HenrikSamuelsson/Killer-Bot-2016/AutodeskWorkspace/robotparts revision 2/bottomSideFrame1.stl

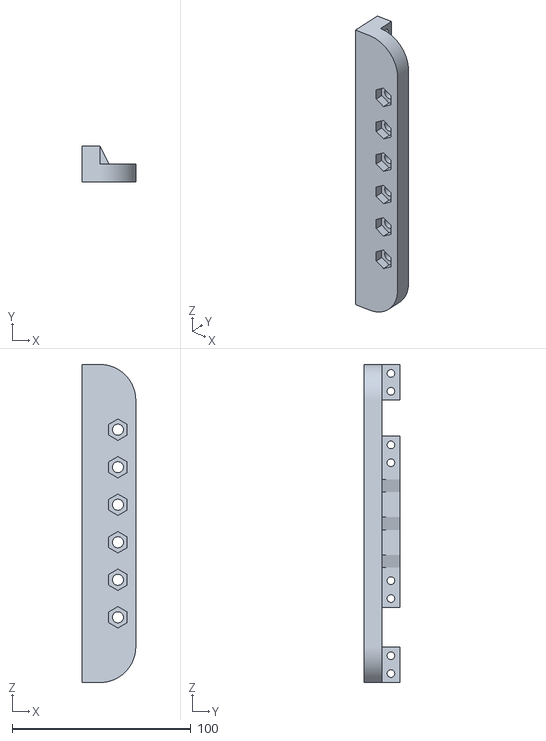
[picture p16: CAD file, 2016-06-10]
AutodeskWorkspace/robotparts revision 2/bottomSideFrame1.stl
30.0 x 20.0 x 178.0
