HenrikSamuelsson/Killer-Bot-2016/printfiles/motorHolder57mm.stl

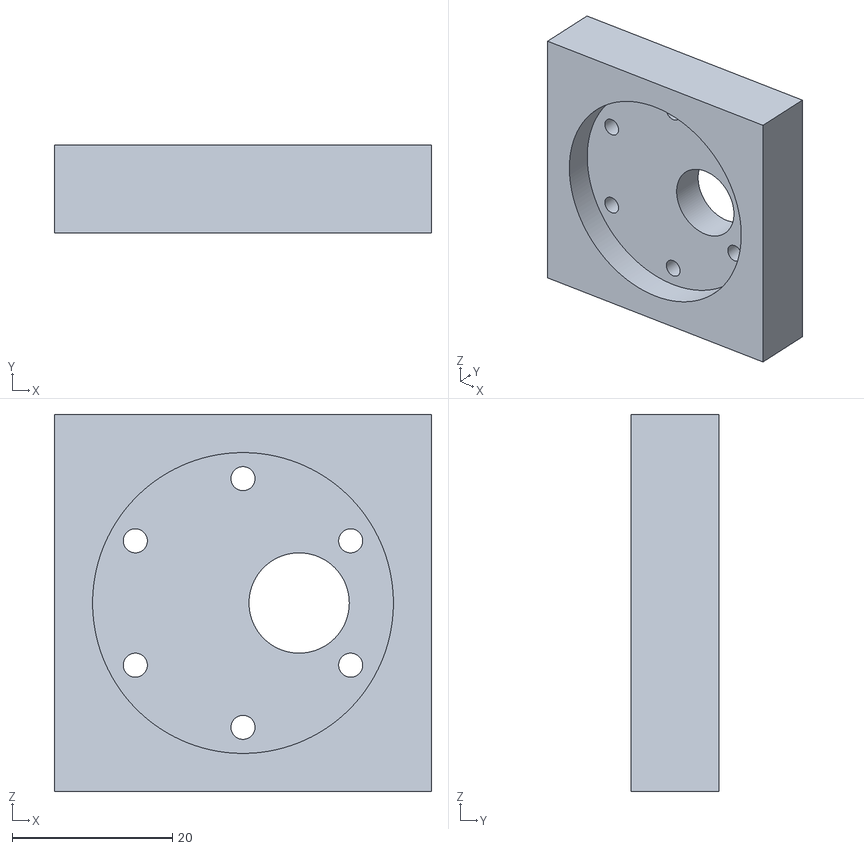
[picture p17: CAD file, 2016-05-10]
printfiles/motorHolder57mm.stl
47.0 x 11.0 x 47.0
