HenrikSamuelsson/Killer-Bot-2016/AutodeskWorkspace/robotparts revision 2/bigOuterSprocket.stl

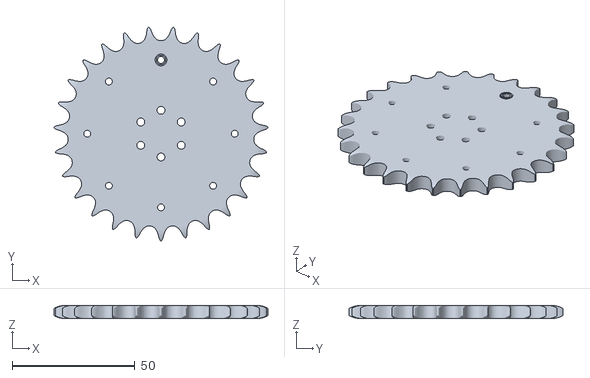
[picture p18: CAD file, 2016-06-10]
AutodeskWorkspace/robotparts revision 2/bigOuterSprocket.stl
87.1 x 86.9 x 5.32
