HenrikSamuelsson/Killer-Bot-2016/printfiles/tracks_outer.stl

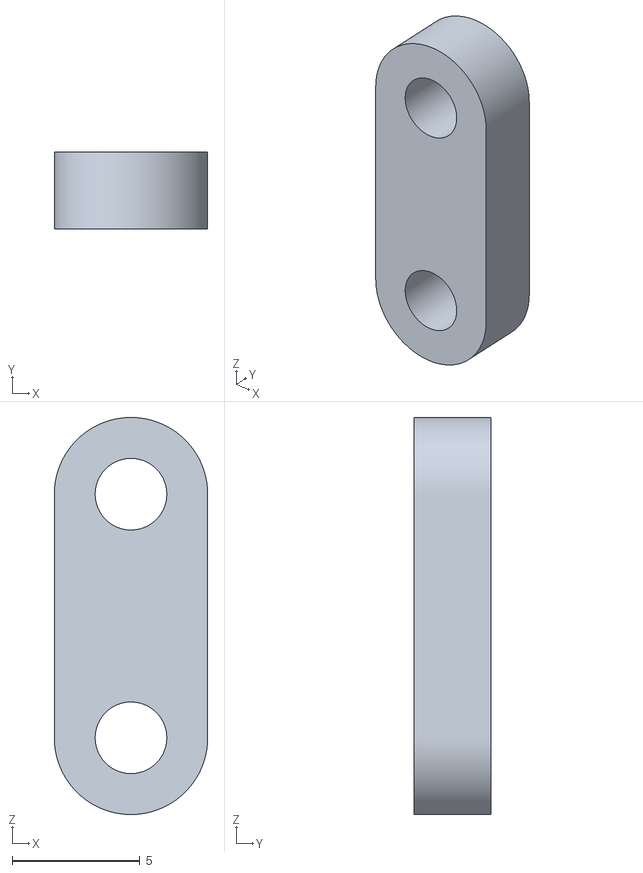
[picture p19: CAD file, 2016-05-04]
printfiles/tracks_outer.stl
6.00 x 3.00 x 15.5
