HenrikSamuelsson/Killer-Bot-2016/AutodeskWorkspace/robotparts revision 2/sideFrame.stl

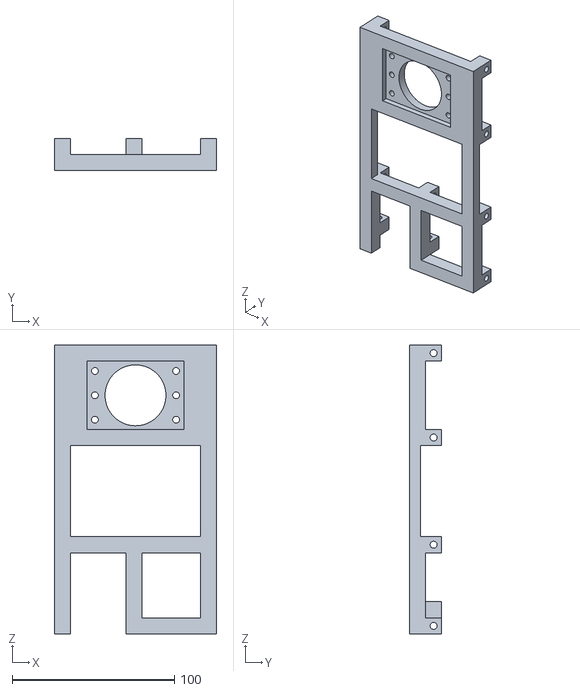
[picture p20: CAD file, 2016-06-08]
AutodeskWorkspace/robotparts revision 2/sideFrame.stl
100.0 x 20.0 x 178.0
