HenrikSamuelsson/Killer-Bot-2016/printfiles/driveSprocket.stl

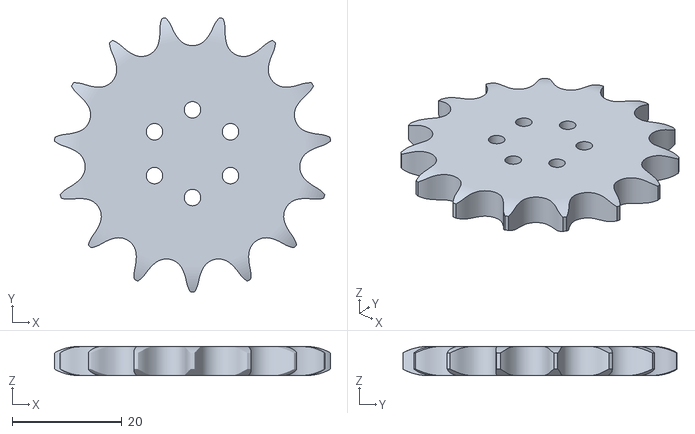
[picture p21: CAD file, 2016-04-27]
printfiles/driveSprocket.stl
50.3 x 50.0 x 5.32
