HenrikSamuelsson/Killer-Bot-2016/printfiles/tracks.stl

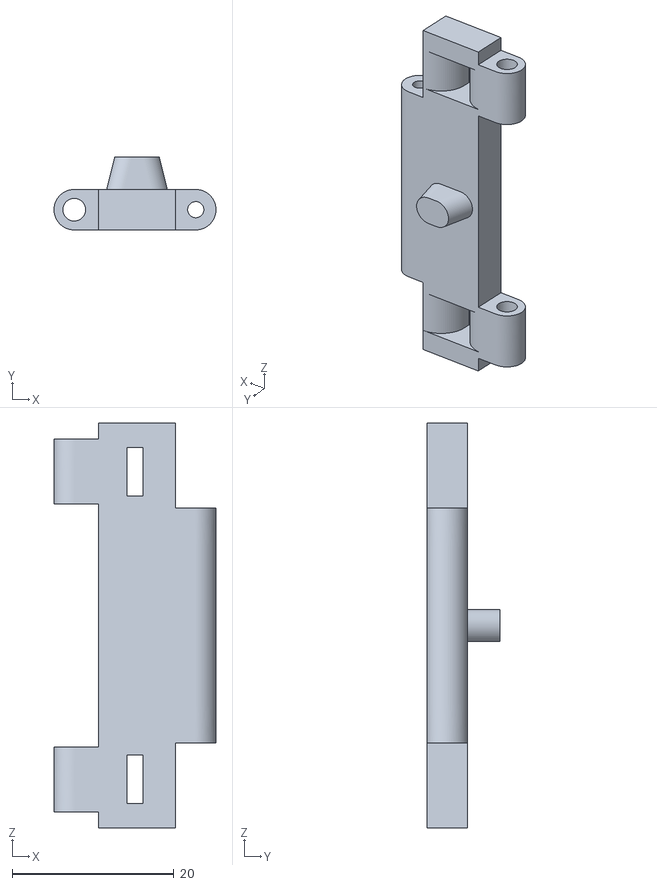
[picture p22: CAD file, 2016-04-20]
printfiles/tracks.stl
20.0 x 9.00 x 50.0
