HenrikSamuelsson/Killer-Bot-2016/AutodeskWorkspace/robotparts revision 2/rollerdistance.stl

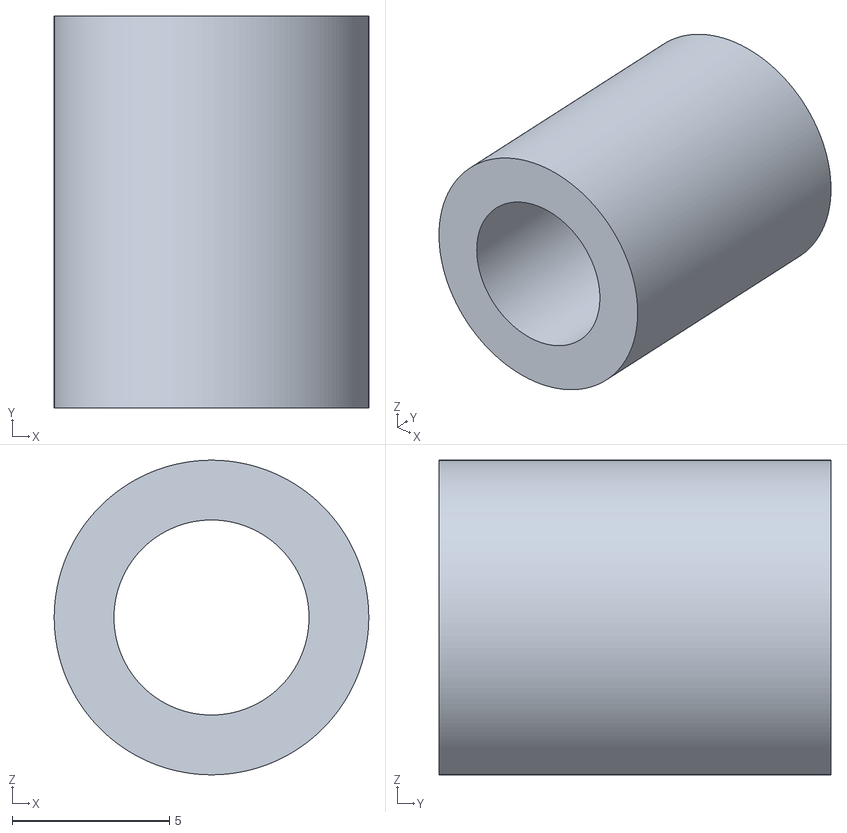
[picture p23: CAD file, 2016-06-06]
AutodeskWorkspace/robotparts revision 2/rollerdistance.stl
10.0 x 12.5 x 10.00
