HenrikSamuelsson/Killer-Bot-2016/printfiles/servoHolderTest1.stl

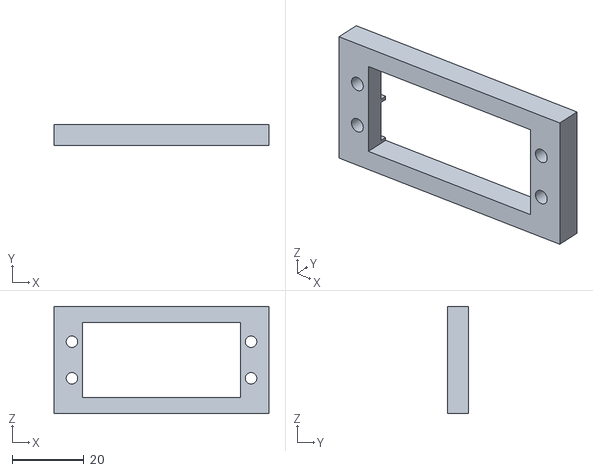
[picture p24: CAD file, 2016-04-17]
printfiles/servoHolderTest1.stl
60.0 x 6.00 x 30.0
