HenrikSamuelsson/Killer-Bot-2016/AutodeskWorkspace/robotparts revision 2/smallSprocketDistance.stl

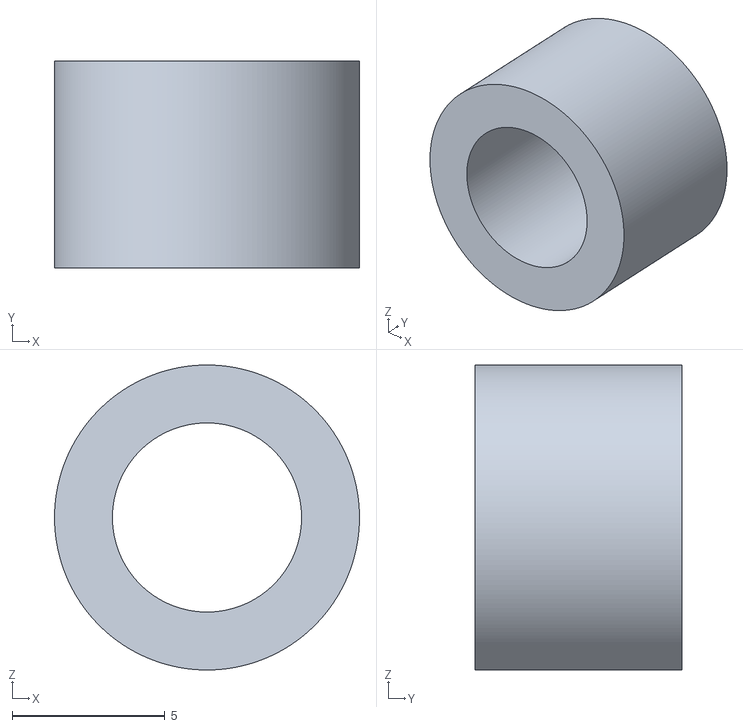
[picture p25: CAD file, 2016-06-06]
AutodeskWorkspace/robotparts revision 2/smallSprocketDistance.stl
10.0 x 6.80 x 10.00
