HenrikSamuelsson/Killer-Bot-2016/AutodeskWorkspace/robotparts revision 2/backFrame.stl

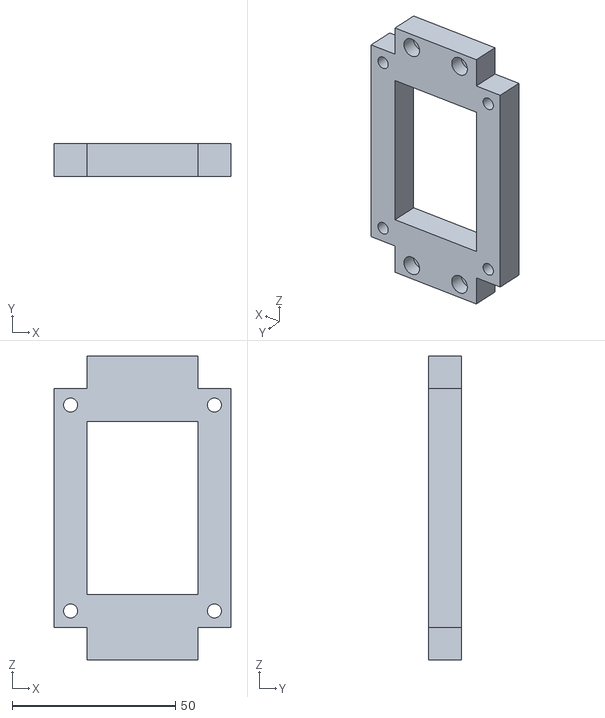
[picture p26: CAD file, 2016-06-06]
AutodeskWorkspace/robotparts revision 2/backFrame.stl
54.0 x 10.0 x 93.0
