HenrikSamuelsson/Killer-Bot-2016/AutodeskWorkspace/robotparts revision 2/smallSprocketFixture.stl

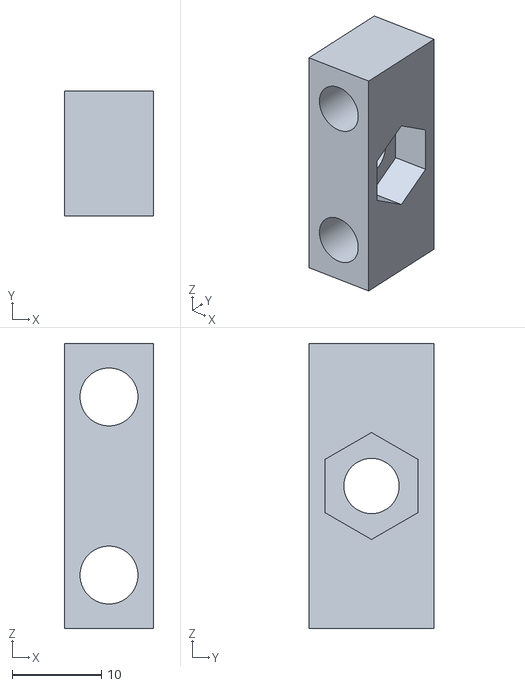
[picture p27: CAD file, 2016-06-06]
AutodeskWorkspace/robotparts revision 2/smallSprocketFixture.stl
10.0 x 14.0 x 32.0
