HenrikSamuelsson/Killer-Bot-2016/AutodeskWorkspace/robotparts revision 2/motorHolder57mmVer2.stl

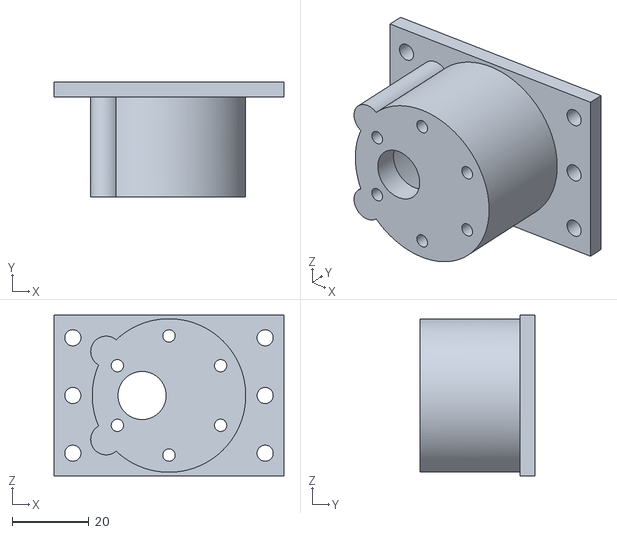
[picture p28: CAD file, 2016-06-02]
AutodeskWorkspace/robotparts revision 2/motorHolder57mmVer2.stl
59.8 x 30.0 x 41.8
