HenrikSamuelsson/Killer-Bot-2016/AutodeskWorkspace/robotparts revision 2/smallSprocketHolder.stl

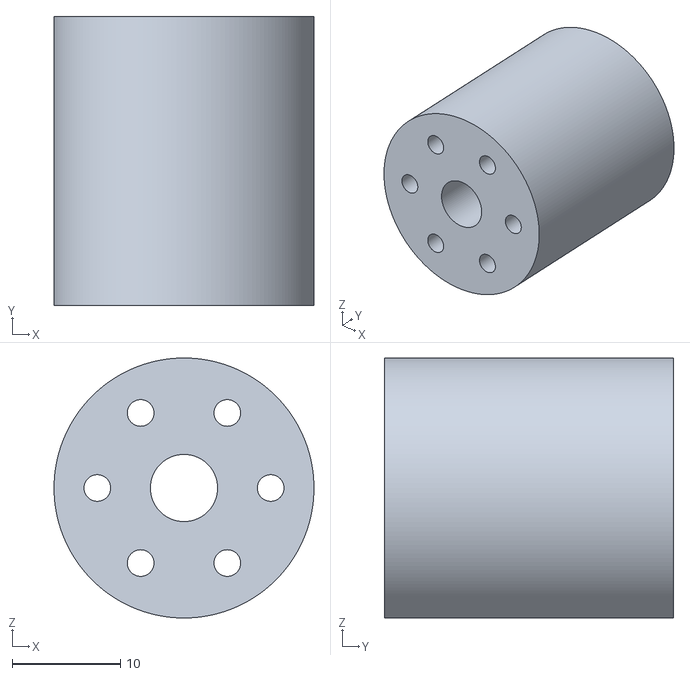
[picture p29: CAD file, 2016-05-29]
AutodeskWorkspace/robotparts revision 2/smallSprocketHolder.stl
24.0 x 26.7 x 24.0
