HenrikSamuelsson/Killer-Bot-2016/AutodeskWorkspace/robotparts revision 2/smallSprocket.stl

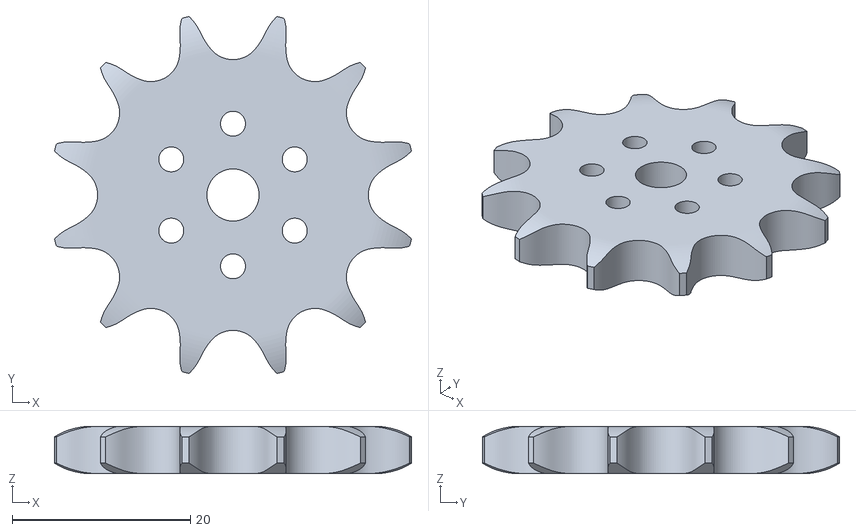
[picture p30: CAD file, 2016-05-28]
AutodeskWorkspace/robotparts revision 2/smallSprocket.stl
40.1 x 40.1 x 5.32
