HenrikSamuelsson/Killer-Bot-2016/AutodeskWorkspace/robotparts revision 2/tracks_center.stl

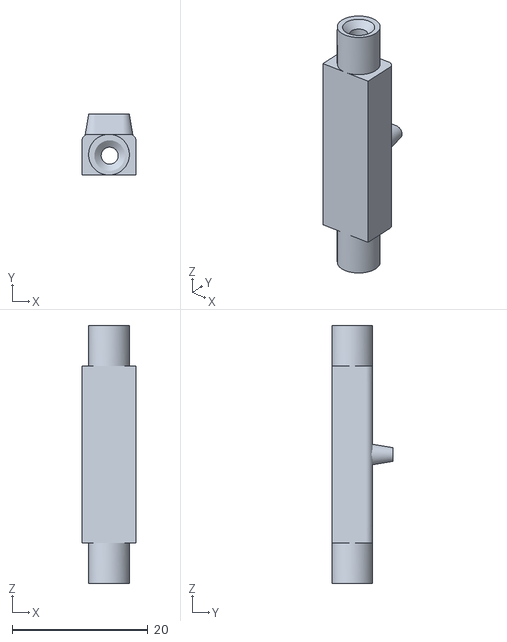
[picture p31: CAD file, 2016-05-08]
AutodeskWorkspace/robotparts revision 2/tracks_center.stl
8.00 x 9.00 x 38.0
